natsfr/pmsre/board/2-layers/fpga.sch

## KiCad design board/2-layers/fpga.sch (2016-07-03)

Schematic: fpga.sch

Parts:
C401, C402, C408, C410, C412, C414: 1u; SM0603
C403, C404, C405, C409, C411, C413, C415: 100n; SM0603
C406, C407: 10n; SM0603
R401, R402, R404: R; SM0603
R403: NE; SM0603
U401: XC3S200A; TQFP_100

Notes on the sheet:
Slave Serial
JTAG
For other mode: UG332 (PDF)
