natsfr/pmsre/board/2-layers/psu.sch

## KiCad design board/2-layers/psu.sch (2016-07-03)

Schematic: psu.sch

Parts:
C301, C302, C303: 4.7u; SM0805
C304, C305: 10uF; SM1210
C306: 4.7nF; SM0603
C307: 0.1uF; SM0603
C308: 10nF; SM0603
C309: 1uF; SM1210
C310: 4.7uF; SM1210
C311, C313, C314, C315: 10uF; SM0805
C312: 1uF; SM0805
L301: 1u; SM1210L
L302: 10uH; IND_7x7x4.5
P301: 12V_Conn; MOL_CONN_2_VH
R301, R307: 10k; SM0603
R302, R303: 200k; SM0603
R304: 100k; SM0603
R305: 4.42k; SM0603
R306: 47k; SM0603
R308: 30.9k; SM0603
U301: MP2128-SOT23; SOT23-5
U302: MP2303_SOIC8E; SO8_WITH_EP
