natsfr/pmsre/board/2-layers/stepper_controller.sch

## KiCad design board/2-layers/stepper_controller.sch (2016-07-03)

Schematic: stepper_controller.sch

Parts:
C101, C102, C103: 0.47u; SM0603
C104, C105, C106, C120: 0.1u; SM0603
C107, C108, C109, C121: 10n; SM0603
C110, C111, C112, C113, C114, C115, C116, C117, C118: 4.7u; SM0805
C119: 1u; SM0603
C122, C123, C124: 100n; SM0603
P101, P102: JTAG; pin_array_6x1
P103, P105, P107: CONN_4; MOL_CONN_4_VH
P104: CONN_8X2; pin_array_8x2
P106: CONN_6X2; pin_array_6x2
P108: CONN_4X2; pin_array_4x2
R101, R102, R103, R104, R105, R106: NE; SM0603
R107, R108, R109: 1M; SM0603
R113, R114, R115, R116, R117, R118: 0.1; SM1206
U101, U102, U103: DRV8825; HTSSOP28_PowerPad
U104: MAX5713/4/5-TSSOP14; SSOP14

Notes on the sheet:
Drive for Lin-Engineering 417-15-03 Coil Current: 1.2A I = Vref/(5*Rsense) Vref = (5*0.1)*1.2
1.158A
GRUIK !
