natsfr/pmsre/board/2-layers/stm_part.sch

## KiCad design board/2-layers/stm_part.sch (2016-07-03)

Schematic: stm_part.sch

Parts:
C201, C202, C203, C204, C205, C206, C207: 1uF; SM0603
C208, C209: CSMALL; SM0603
D202: BUSY_ORANGE; LED-0805
D203: POWER_GREEN; LED-0805
J201: USB_OTG; Molex_54819-0572
P201: CONN_2X2; pin_array_2x2
P202: CONN_2; pin_array_2x1
R201, R210: 0; SM0603
R202, R209: 10k; SM0603
R204, R205: ?; SM0603
R206: 1.5k; SM0603
R207, R208: 22; SM0603
U201: STM32F103RG_LQFP64; LQFP_64
X201: TXC_50X32_AB; XTAL_5.0x3.2mm

Notes on the sheet:
Bootmode: - BOOT1: X - BOOT0: 0 -> User Flash Memory - BOOT1: 0 - BOOT0: 1 -> System Memory - BOOT1: 1 - BOOT0: 1 -> Embedded SRAM
SPI2
SPI1
USART2
