natsfr/pmsre/soft/mutekh/boards/fpga.c

#include "fpga.h"

const uint8_t fpga_stream[] = {
  0xff, 0xff, 0xff, 0xff, 0xff, 0xff, 0xff, 0xff, 0xff,
  0xff, 0xff, 0xff, 0xff, 0xff, 0xff, 0xff, 0xff, 0xff, 0xff, 0xff, 0xff, 0xff, 0xff, 0xff, 0xff,
  0xff, 0xff, 0xff, 0xff, 0xff, 0xff, 0xff,  0xaa, 0x99, 0x30, 0xa1, 0x00, 0x07, 0x20, 0x00, 0x31, 
  0x61, 0x09, 0xee, 0x33, 0x21, 0x3c, 0x0f, 0x31, 0xa1, 0x00, 0x49, 0x31, 0x41, 0x2f, 0x08, 0x31, 
  0xc2, 0x02, 0x21, 0x00, 0x93, 0x30, 0xe1, 0xff, 0xcf, 0x30, 0xc1, 0x00, 0x81, 0x31, 0x81, 0x08, 
  0x81, 0x32, 0x01, 0x00, 0x1f, 0x32, 0xc1, 0x00, 0x05, 0x32, 0xe1, 0x00, 0x04, 0x32, 0xa1, 0x00, 
  0x0e, 0x32, 0x61, 0x00, 0x00, 0x32, 0x81, 0x00, 0x00, 0x33, 0x41, 0x18, 0xf2, 0x33, 0x62, 0x00, 
  0x00, 0x00, 0x00, 0x30, 0x22, 0x00, 0x00, 0x00, 0x00, 0x30, 0xa1, 0x00, 0x01, 0x50, 0x60, 0x00, 
  0x00, 0x6a, 0x60, 0x00, 0x00, 0x00, 0x20, 0x00, 0x00, 0x00, 0x00, 0x00, 0x00, 0x00, 0x00, 0x00, 
  0x00, 0x00, 0x00, 0x00, 0x00, 0x00, 0x00, 0x00, 0x00, 0x00, 0x00, 0x00, 0x00, 0x00, 0x00, 0x00, 
  0x00, 0x00, 0x00, 0x00, 0x00, 0x00, 0x00, 0x00, 0x00, 0x00, 0x00, 0x00, 0x00, 0x00, 0x00, 0x00, 
  0x00, 0x00, 0x00, 0x00, 0x00, 0x00, 0x00, 0x00, 0x00, 0x00, 0x00, 0x00, 0x00, 0x00, 0x00, 0x00, 
  0x00, 0x00, 0x00, 0x00, 0x00, 0x00, 0x00, 0x00, 0x00, 0x00, 0x00, 0x00, 0x00, 0x00, 0x00, 0x00, 
  0x00, 0x00, 0x00, 0x00, 0x00, 0x00, 0x00, 0x00, 0x00, 0x00, 0x00, 0x00, 0x00, 0x00, 0x00, 0x00, 
  0x00, 0x00, 0x00, 0x00, 0x00, 0x00, 0x00, 0x00, 0x00, 0x00, 0x00, 0x00, 0x00, 0x00, 0x00, 0x00, 
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
  0x00, 0x00, 0x00, 0x00, 0x00, 0x00, 0x00, 0x00, 0x00, 0x00, 0x00, 0x00, 0x00, 0x00, 0x00, 0x00, 
  0x00, 0x00, 0x10, 0x00, 0x00, 0x00, 0x00, 0x00, 0x00, 0x00, 0x00, 0x00, 0x00, 0x00, 0x10, 0x00, 
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
};

const size_t fpga_stream_size = sizeof(fpga_stream);
